goog-yaml/VIPER/KiCAD/ref/SX1262 mbed shield with Murata IPD/gerber/layers_description_pcb_e588v01a.docx

Layers description: PCB_E588V01A - 4-Layers FR4 1.00mm

Very Important !!!

Top

SX126xMB2xAS_e588v01a.GTO – Silkscreen Top

SX126xMB2xAS_e588v01a.GTS - Solder_mask Top

SX126xMB2xAS_e588v01a.GTL – Signal_top (35um Copper)

Isolation – FR4 (0.15mm)

SX126xMB2xAS_e588v01a.G1 – Internal signal layer (35um Copper)

Isolation – FR4 (approximately ~0.58mm)

SX126xMB2xAS_e588v01a.G2 – Internal signal layer (35um Copper)

Isolation – FR4 (0.15mm)

SX126xMB2xAS_e588v01a.GBL – Signal Bottom (35um Copper)

SX126xMB2xAS_e588v01a.GBS - Solder_mask Bottom

SX126xMB2xAS_e588v01a.GBO – Silkscreen Bottom

Bottom

Other Layers:

SX126xMB2xAS_e588v01a.GM3 – Drawing -> Origin & size of the PCB

SX126xMB2xAS_e588v01a.GTP – Top_Paste_Mask (Single module - not used for PCB manufacturing)

Semtech Neuchatel 02/12/2019
